fm4dd/pmod-7seg9/images/7seg9-protocol-osc.png

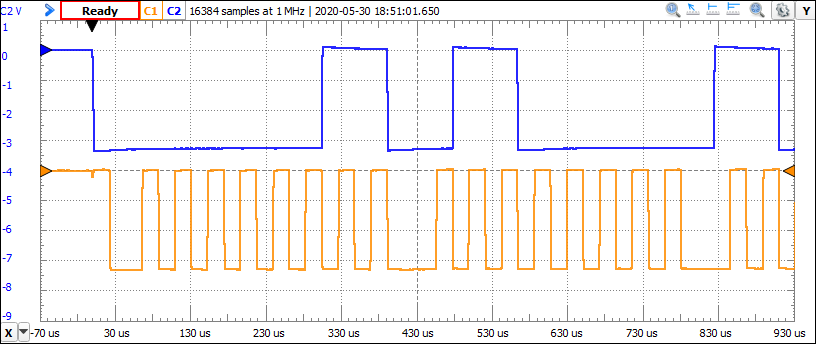
images/7seg9-protocol-osc.png
