fm4dd/pmod-7seg9/examples/gatemate/pmod_7seg9_3/src/debounce.v

// -------------------------------------------------------
// Simplified Debounce Module with Simulation Bypass
// -------------------------------------------------------
module debounce(
    input  wire clk,
    input  wire in,
    output reg  press_edge
);
    // -------------------------------------------------------
    // If -DSIMULATION is passed to iverilog, we use
    // 10 cycles. Otherwise use 20ms (200k cycles @ 10MHz).
    // -------------------------------------------------------
    `ifdef SIMULATION
        localparam CNT_20MS = 10;
    `else
        localparam CNT_20MS = 200_000;    
    `endif

    reg [17:0] stable_cnt = 0;
    reg button_sync_0, button_sync_1;
    reg button_stable = 0;
    reg button_prev = 0;

    always @(posedge clk) begin
        // Two-stage synchronizer to prevent metastability
        button_sync_0 <= in;
        button_sync_1 <= button_sync_0;

        if (button_sync_1 == button_stable) begin
            stable_cnt <= 0;
        end else begin
            stable_cnt <= stable_cnt + 1;
            if (stable_cnt >= CNT_20MS) begin
                button_stable <= button_sync_1;
                stable_cnt <= 0;
            end
        end

        press_edge <= 0;
        button_prev <= button_stable;

        // Pulse logic: triggers on the rising edge of the stable signal
        if (button_stable && !button_prev) begin
            press_edge <= 1;
        end
    end
endmodule
